Devnol/The-Summit/Image/Printed_side.jpg

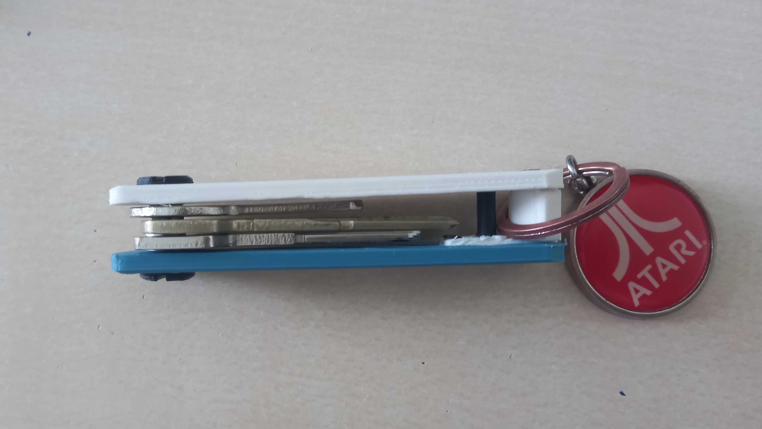
Image/Printed_side.jpg
